alex-ong/BishiBashiLaserCut/images/feet.jpg

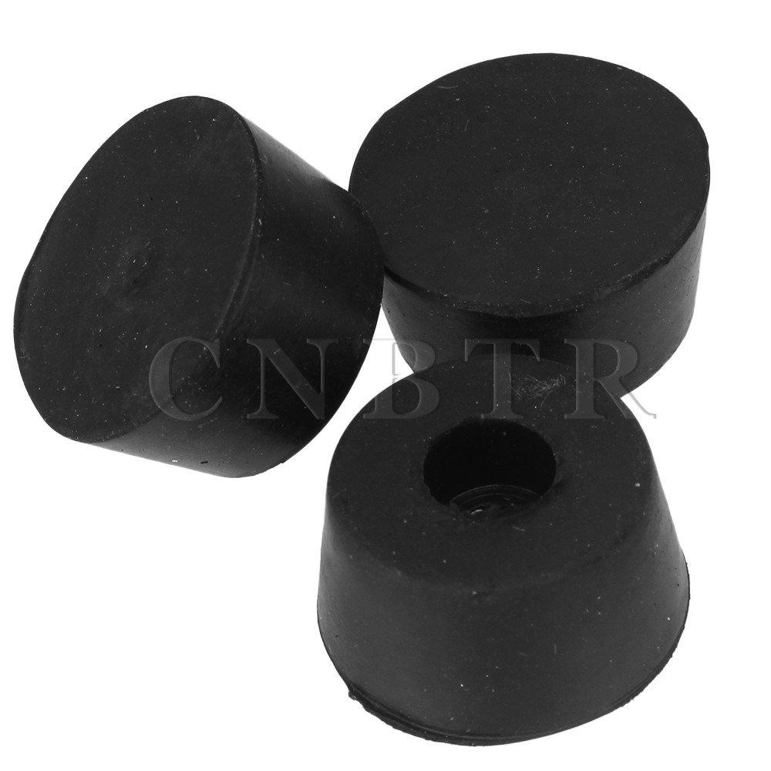
images/feet.jpg
