alex-ong/BishiBashiLaserCut/images/Green.jpg

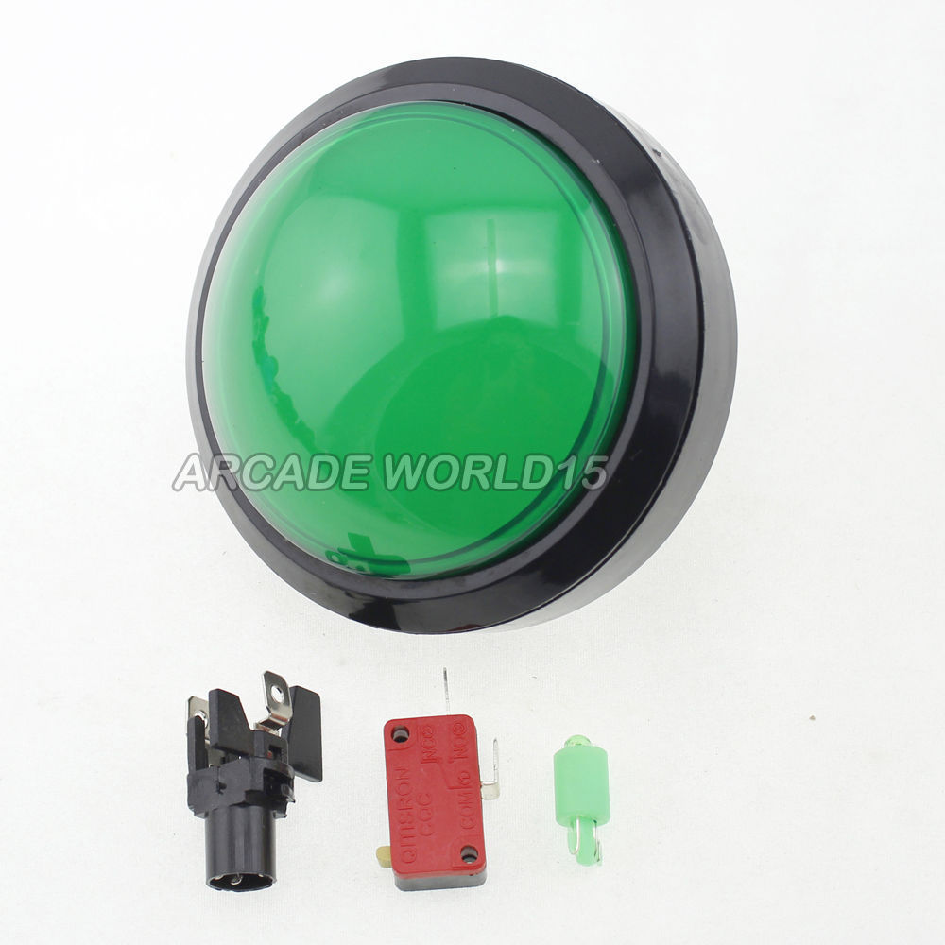
images/Green.jpg
