alex-ong/BishiBashiLaserCut/images/hexnut.jpg

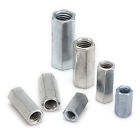
images/hexnut.jpg
