alex-ong/BishiBashiLaserCut/images/m3kit.jpg

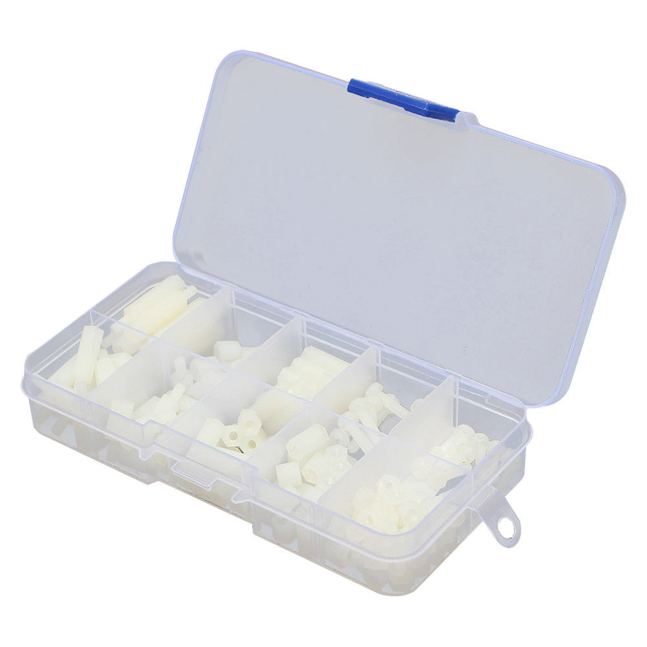
images/m3kit.jpg
