alex-ong/BishiBashiLaserCut/images/panhead.jpg

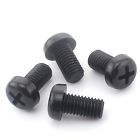
images/panhead.jpg
