alex-ong/BishiBashiLaserCut/images/spacer.jpg

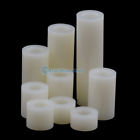
images/spacer.jpg
