alex-ong/BishiBashiLaserCut/images/printercable.jpg

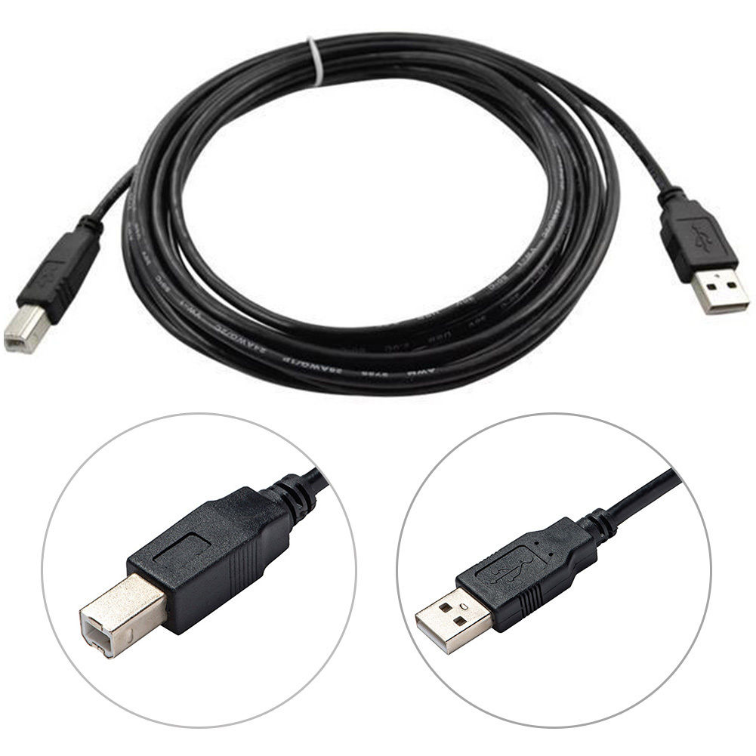
images/printercable.jpg
